ionutmantu8/InkTime-Project/Images/Complete_Device.png

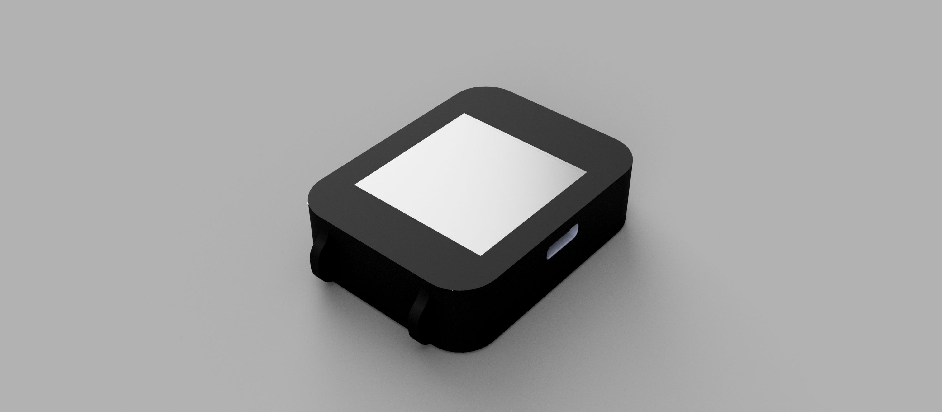
Images/Complete_Device.png
